Hayo-Tee/power-control/pictures/IMG_20250816_132007.jpg

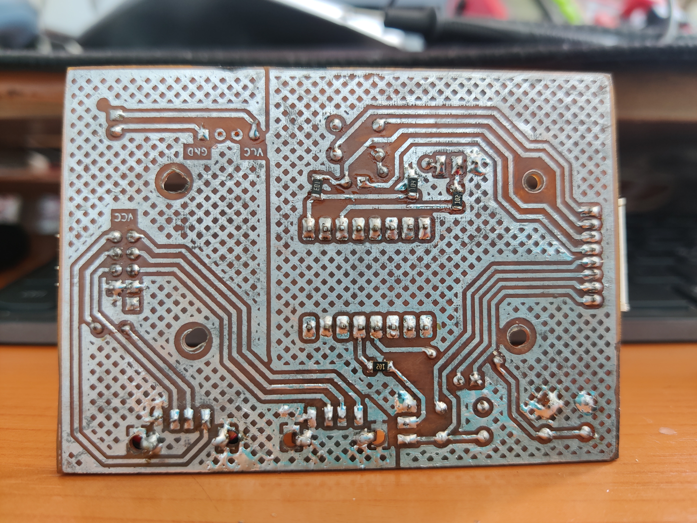
pictures/IMG_20250816_132007.jpg
