Hayo-Tee/power-control/pictures/IMG_20250816_132037.jpg

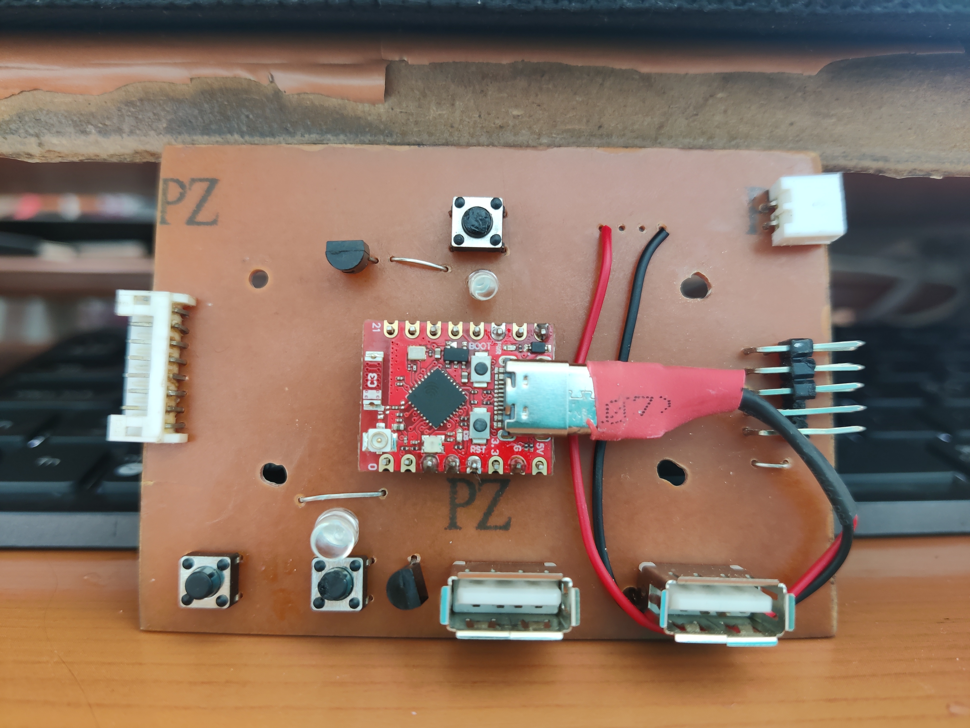
pictures/IMG_20250816_132037.jpg
